atopile/cell-sim/elec/cell-card/parts/UNI_ROYAL_0603WAF1002T5E/R0603.STEP

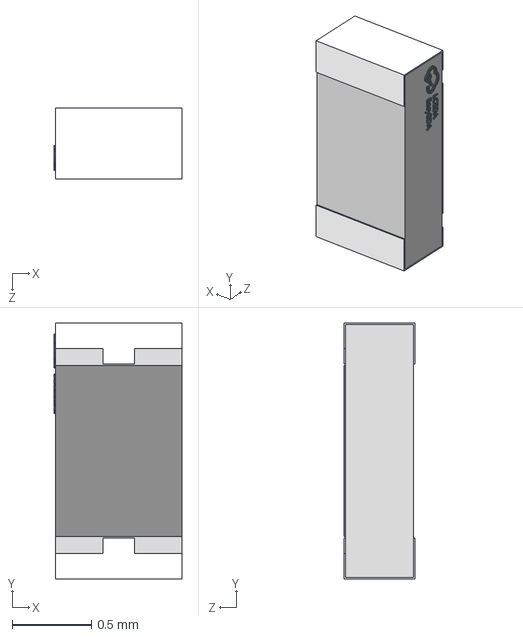
[picture p5: CAD file, 2026-02-27]
elec/cell-card/parts/UNI_ROYAL_0603WAF1002T5E/R0603.STEP
0.81 x 1.62 x 0.45 mm
