atopile/cell-sim/elec/cell-card/parts/UNI_ROYAL_0805W4F500MT5E/R0805_L2.0-W1.3-H0.6.step

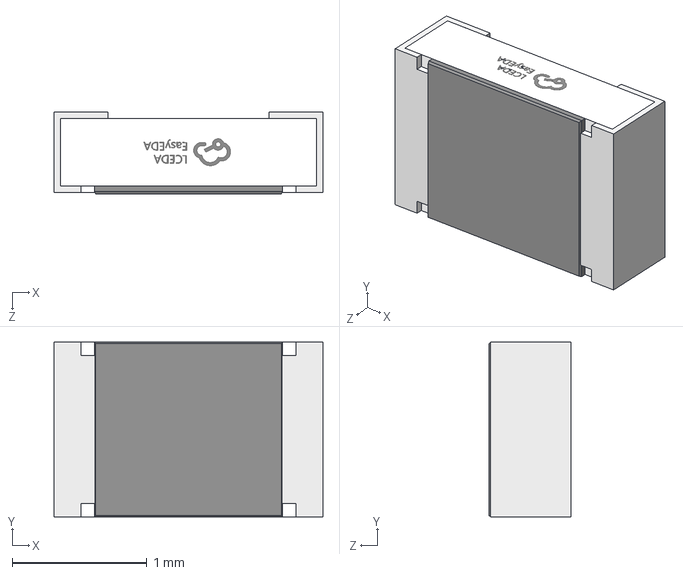
[picture p6: CAD file, 2026-02-27]
elec/cell-card/parts/UNI_ROYAL_0805W4F500MT5E/R0805_L2.0-W1.3-H0.6.step
2.00 x 1.30 x 0.61 mm
