atopile/cell-sim/elec/packages/buttons/parts/ALPSALPINE_SKRPACE010/KEY-SMD_4P-L4.2-W3.2-H2.5-LS4.6-P2.2.step

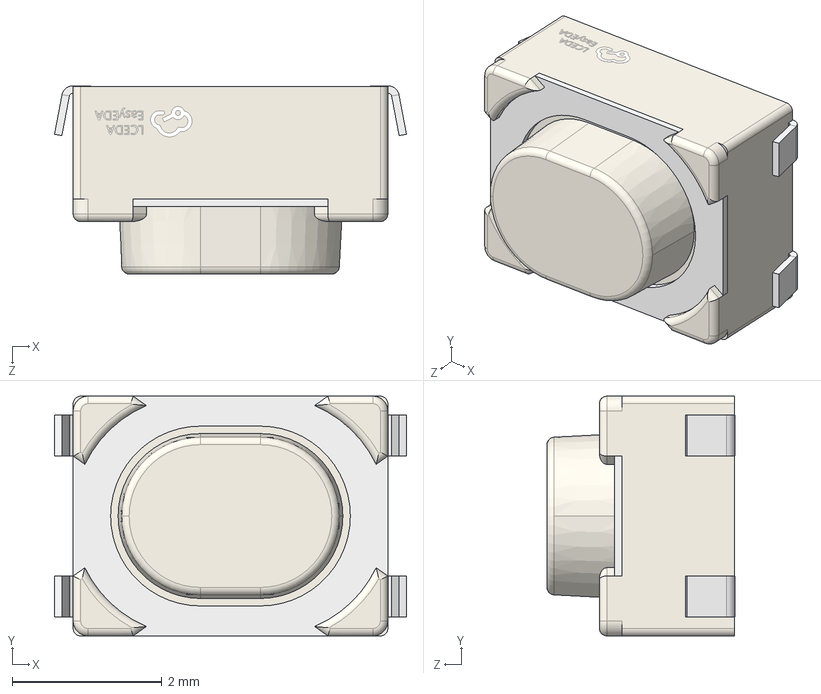
[picture p7: CAD file, 2026-03-11]
elec/packages/buttons/parts/ALPSALPINE_SKRPACE010/KEY-SMD_4P-L4.2-W3.2-H2.5-LS4.6-P2.2.step
4.70 x 3.20 x 2.51 mm
