atopile/cell-sim/elec/packages/buttons/parts/ALPSALPINE_SKTDLDE010/KEY-SMD_SKTDLDE010.step

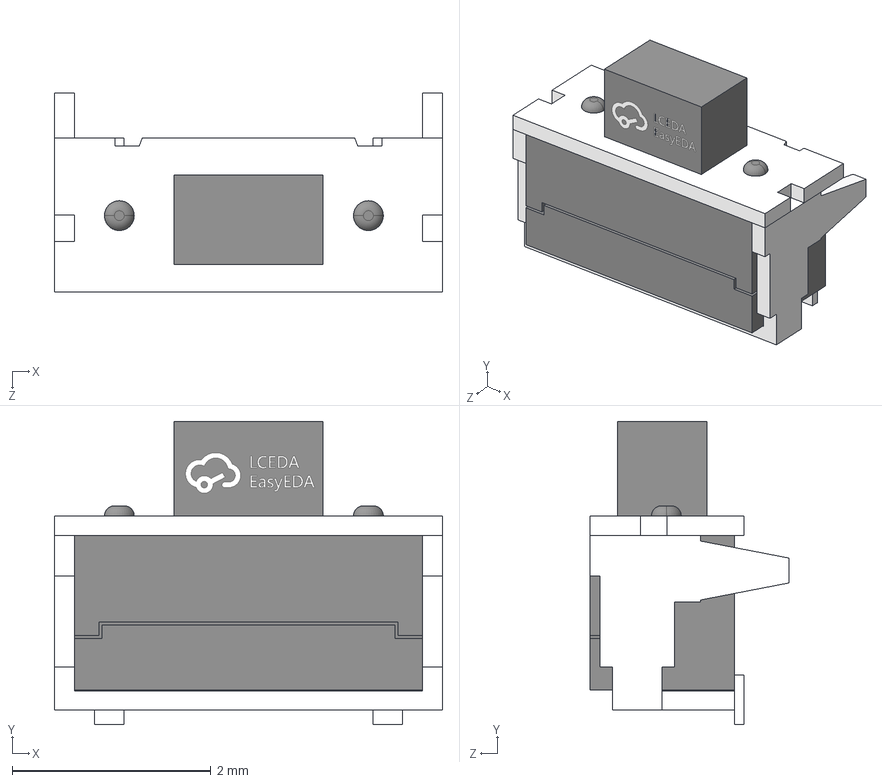
[picture p8: CAD file, 2026-03-11]
elec/packages/buttons/parts/ALPSALPINE_SKTDLDE010/KEY-SMD_SKTDLDE010.step
3.90 x 3.05 x 2.00 mm
