atopile/cell-sim/elec/packages/indicator-leds/parts/Diodes_Incorporated_B230A_13_F/SMA_L4.4-W2.6-LS5.0-RD.step

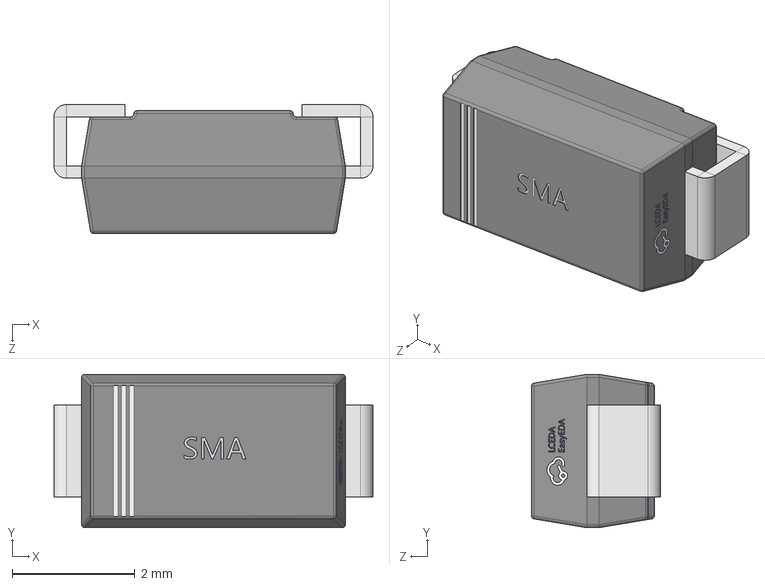
[picture p9: CAD file, 2026-03-11]
elec/packages/indicator-leds/parts/Diodes_Incorporated_B230A_13_F/SMA_L4.4-W2.6-LS5.0-RD.step
5.20 x 2.50 x 2.10 mm
