atopile/cell-sim/elec/packages/indicator-leds/parts/Hubei_KENTO_Elec_Blue_light_0603/LED0603-RD-YELLOW.STEP

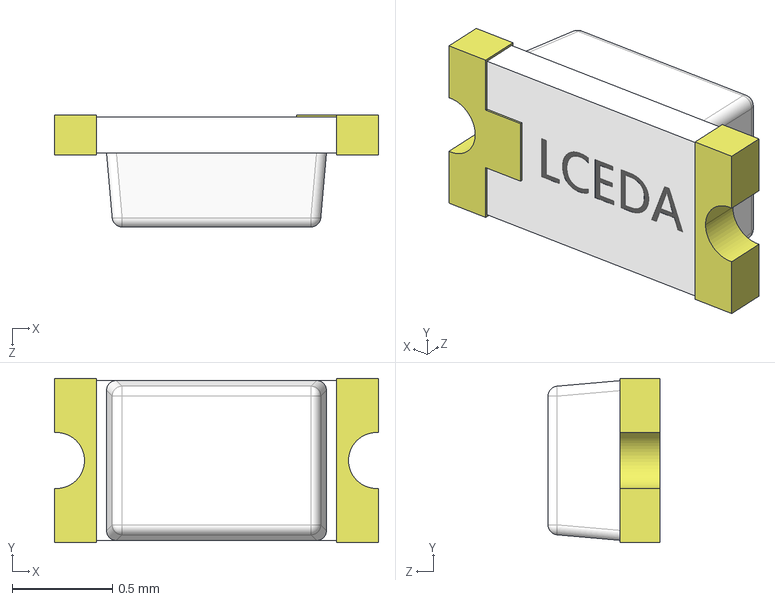
[picture p10: CAD file, 2026-03-11]
elec/packages/indicator-leds/parts/Hubei_KENTO_Elec_Blue_light_0603/LED0603-RD-YELLOW.STEP
1.62 x 0.82 x 0.56 mm
