atopile/cell-sim/elec/packages/indicator-leds/parts/Hubei_KENTO_Elec_KT_0603W/LED0603-RD_ORANGE.STEP

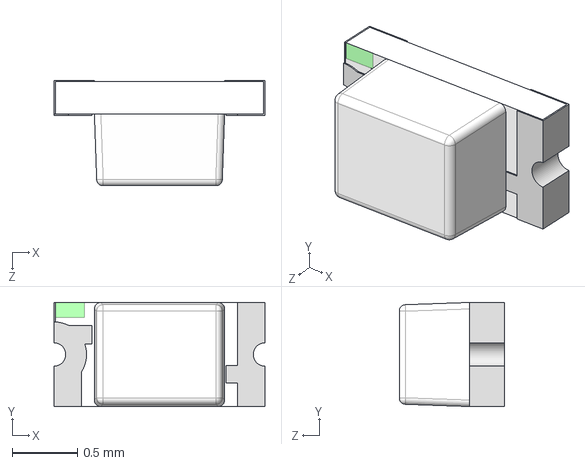
[picture p11: CAD file, 2026-03-11]
elec/packages/indicator-leds/parts/Hubei_KENTO_Elec_KT_0603W/LED0603-RD_ORANGE.STEP
1.62 x 0.8 x 0.81 mm
