atopile/cell-sim/elec/packages/indicator-leds/parts/Hubei_KENTO_Elec_KT_0603Y/LED0603-RD_BLUE.STEP

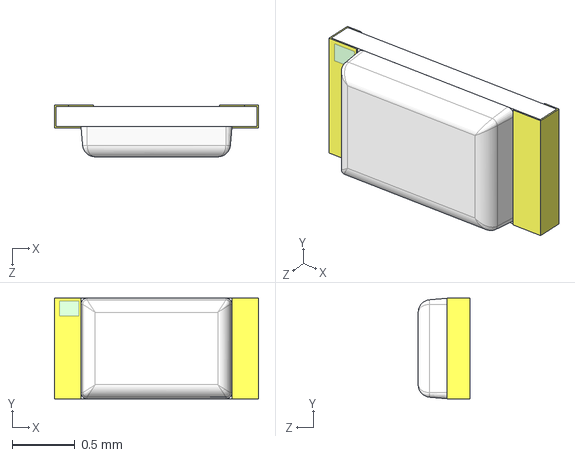
[picture p12: CAD file, 2026-03-11]
elec/packages/indicator-leds/parts/Hubei_KENTO_Elec_KT_0603Y/LED0603-RD_BLUE.STEP
1.62 x 0.8 x 0.41 mm
