atopile/cell-sim/elec/packages/indicator-leds/parts/MDD_Microdiode_Electronics_M7/SMA_L4.3-W2.6-LS5.2-RD.step

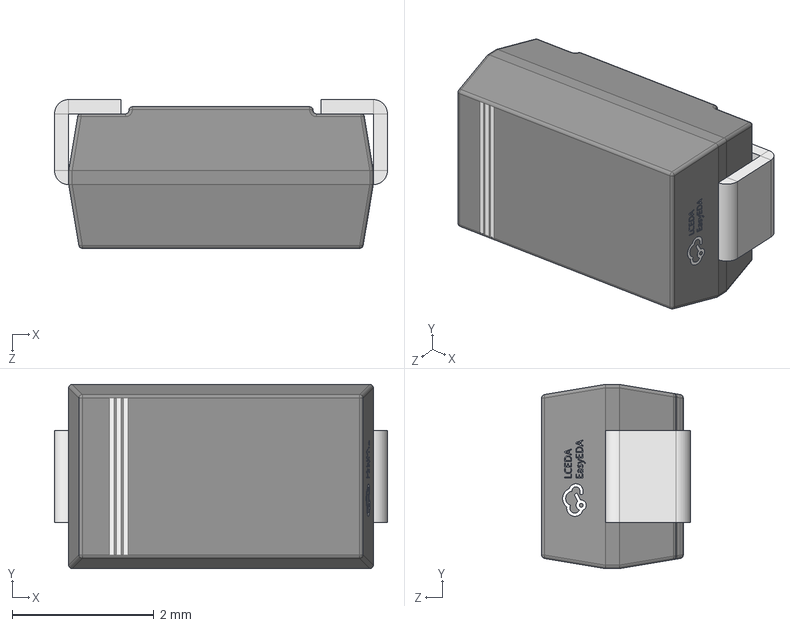
[picture p13: CAD file, 2026-03-11]
elec/packages/indicator-leds/parts/MDD_Microdiode_Electronics_M7/SMA_L4.3-W2.6-LS5.2-RD.step
4.70 x 2.60 x 2.10 mm
