atopile/cell-sim/elec/packages/microchip-emc2101/parts/Microchip_Tech_EMC2101_R_ACZL_TR/MSOP-8_L3.0-W3.0-H1.1-LS4.9-P0.65.step

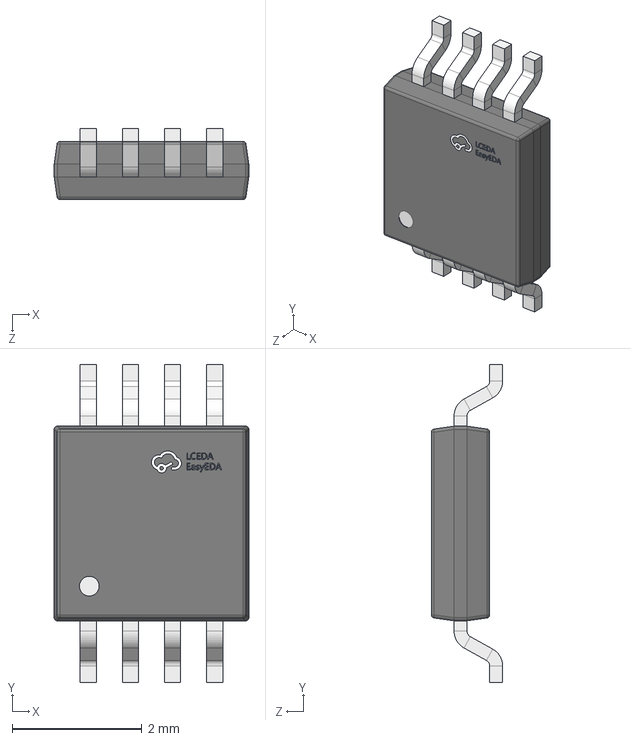
[picture p14: CAD file, 2026-03-11]
elec/packages/microchip-emc2101/parts/Microchip_Tech_EMC2101_R_ACZL_TR/MSOP-8_L3.0-W3.0-H1.1-LS4.9-P0.65.step
3.00 x 4.90 x 1.10 mm
