atopile/cell-sim/elec/packages/microchip-emc2101/parts/YAGEO_CC0603KRX7R9BB104/C0603_L1.6-W0.8-H0.8.step

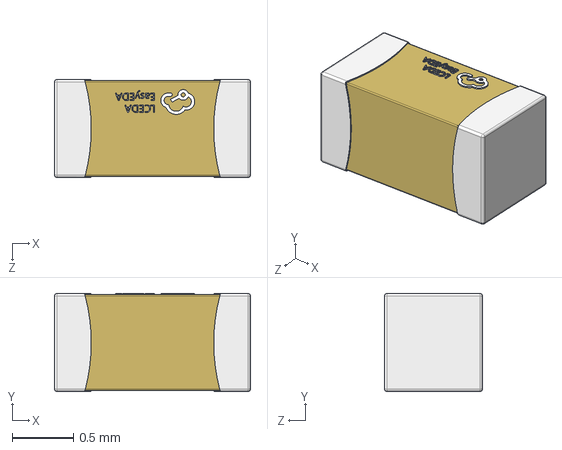
[picture p15: CAD file, 2026-02-27]
elec/packages/microchip-emc2101/parts/YAGEO_CC0603KRX7R9BB104/C0603_L1.6-W0.8-H0.8.step
1.60 x 0.8 x 0.8 mm
