atopile/cell-sim/elec/packages/microchip-lan8742a/parts/Microchip_Tech_LAN8742A_CZ_TR/QFN-24_L4.0-W4.0-P0.50-TL-EP2.1.step

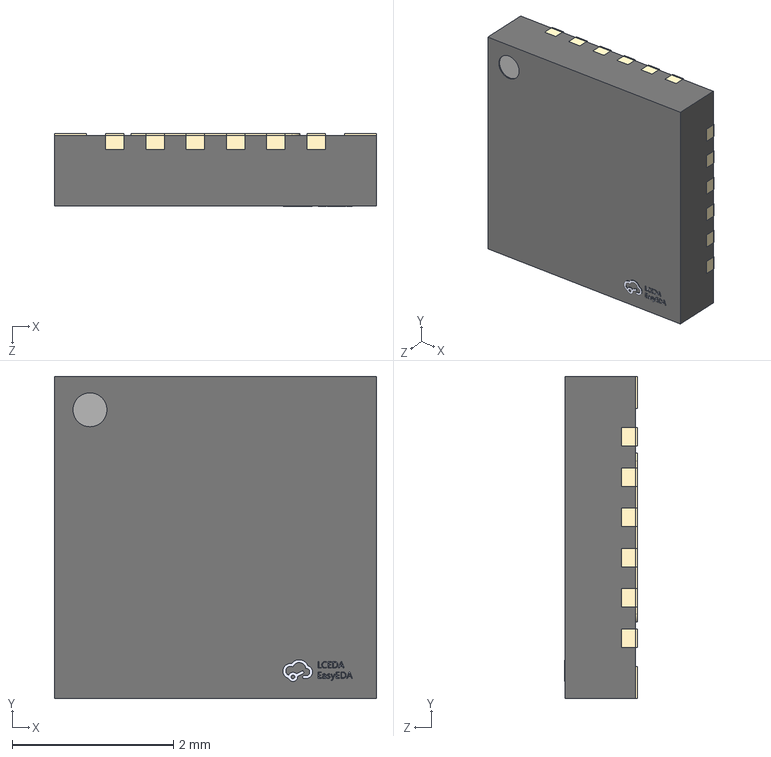
[picture p16: CAD file, 2026-02-27]
elec/packages/microchip-lan8742a/parts/Microchip_Tech_LAN8742A_CZ_TR/QFN-24_L4.0-W4.0-P0.50-TL-EP2.1.step
4.00 x 4.00 x 0.91 mm
