atopile/cell-sim/elec/packages/microchip-lan8742a/parts/Yangxing_Tech_X322525MRB4SI/OSC-SMD_4P-L3.2-W2.5-CJ13-320001210A20.step

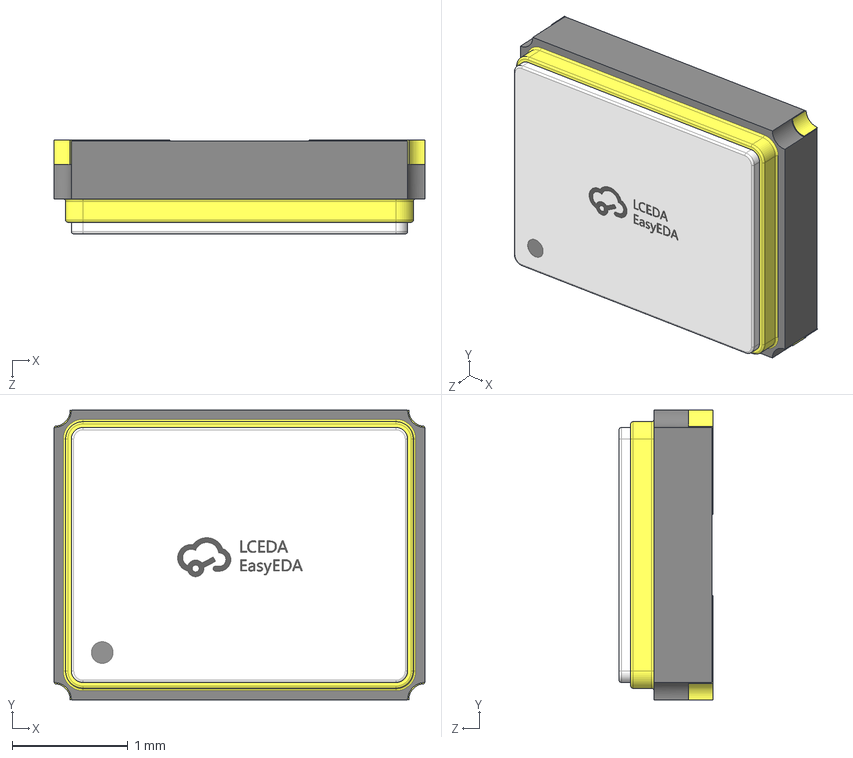
[picture p17: CAD file, 2026-02-27]
elec/packages/microchip-lan8742a/parts/Yangxing_Tech_X322525MRB4SI/OSC-SMD_4P-L3.2-W2.5-CJ13-320001210A20.step
3.20 x 2.50 x 0.811 mm
