atopile/cell-sim/elec/packages/microchip-mcp23017/parts/Microchip_Tech_MCP23017T_E_ML/QFN-28_L6.0-W6.0-P0.65-BL-EP3.7.step

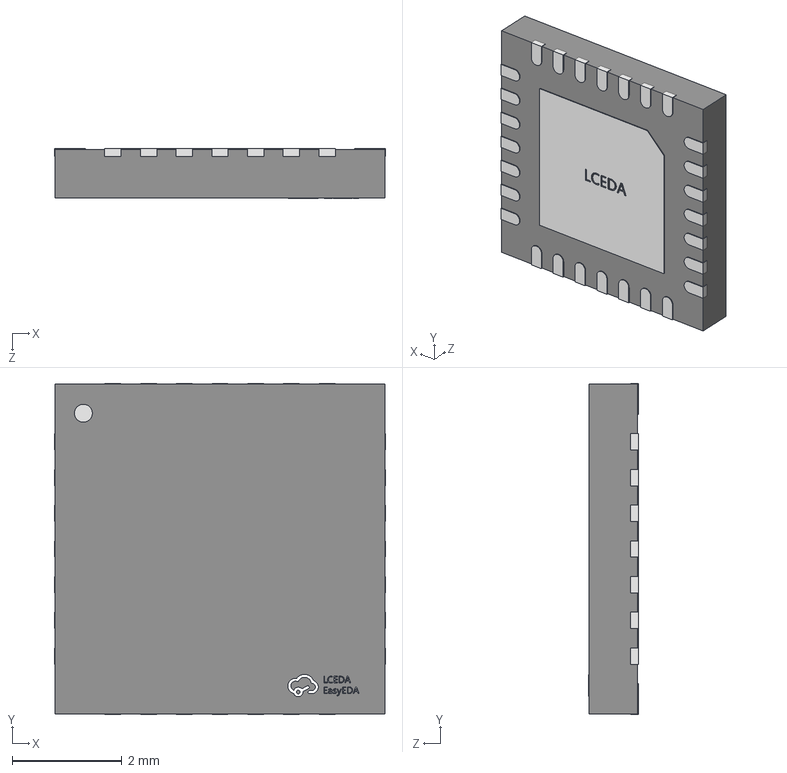
[picture p18: CAD file, 2026-03-11]
elec/packages/microchip-mcp23017/parts/Microchip_Tech_MCP23017T_E_ML/QFN-28_L6.0-W6.0-P0.65-BL-EP3.7.step
6.02 x 6.02 x 0.91 mm
