atopile/cell-sim/elec/packages/microchip-mcp3221/parts/Microchip_Tech_MCP3221A5T_I_OT/SOT-23-5_L2.9-W1.6-H1.1-LS2.8-P0.95.step

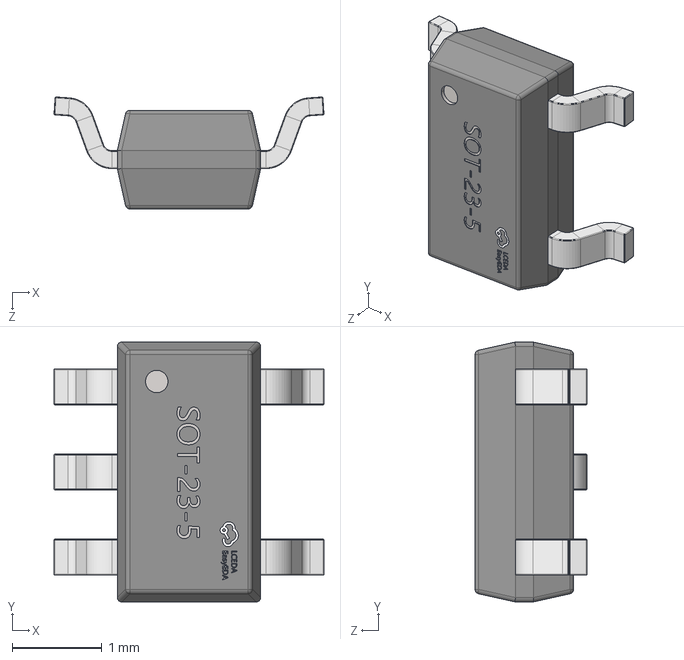
[picture p19: CAD file, 2026-02-27]
elec/packages/microchip-mcp3221/parts/Microchip_Tech_MCP3221A5T_I_OT/SOT-23-5_L2.9-W1.6-H1.1-LS2.8-P0.95.step
3.01 x 2.90 x 1.25 mm
