atopile/cell-sim/elec/packages/microchip-mcp4725/parts/Microchip_Tech_MCP3421A0T_E_CH/SOT-23-6_L2.9-W1.6-H1.5-LS2.8-P0.95.step

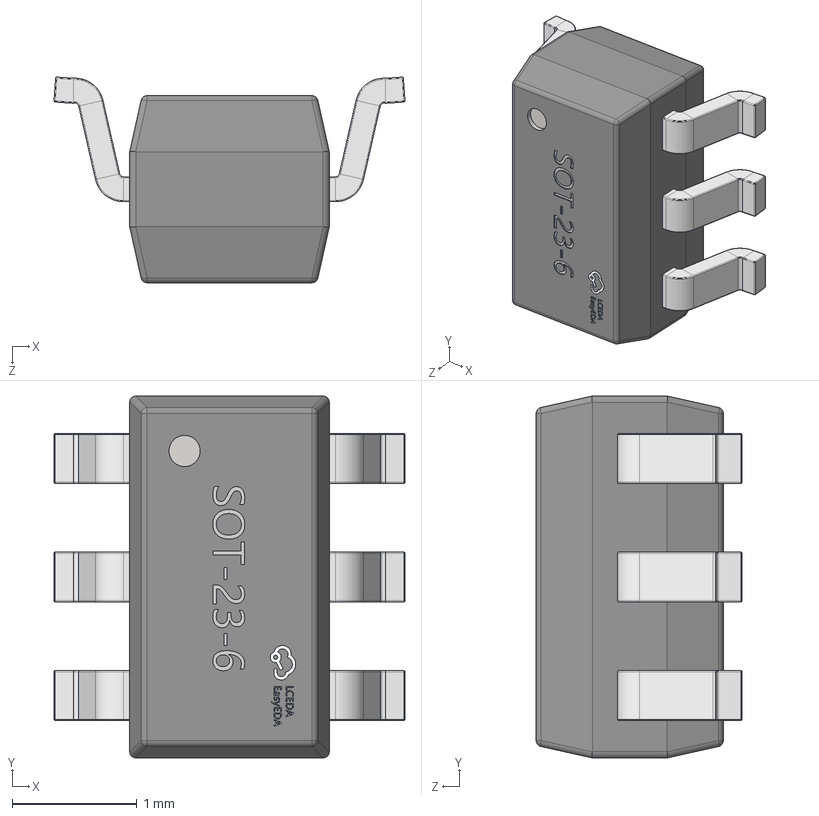
[picture p20: CAD file, 2026-02-27]
elec/packages/microchip-mcp4725/parts/Microchip_Tech_MCP3421A0T_E_CH/SOT-23-6_L2.9-W1.6-H1.5-LS2.8-P0.95.step
2.81 x 2.90 x 1.65 mm
