atopile/cell-sim/elec/packages/programming-headers/parts/Hanbo_Electronic_HB_PH9_12725PB2GOB/HDR-SMD_10P-P1.27-V-M-R2-C5-LS5.3.STEP

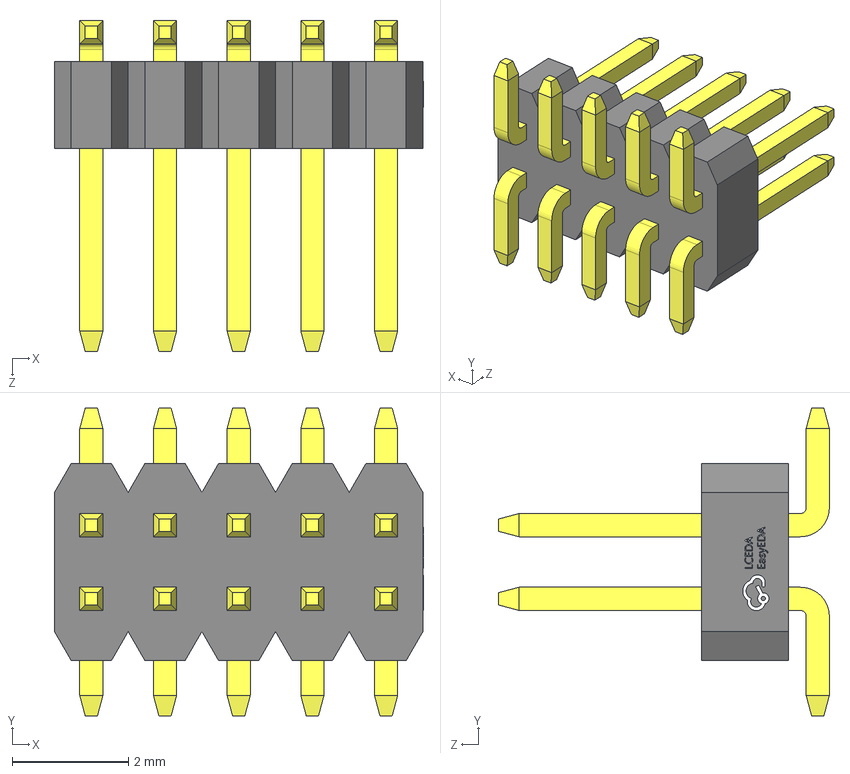
[picture p21: CAD file, 2026-03-11]
elec/packages/programming-headers/parts/Hanbo_Electronic_HB_PH9_12725PB2GOB/HDR-SMD_10P-P1.27-V-M-R2-C5-LS5.3.STEP
6.36 x 5.30 x 5.70 mm
