atopile/cell-sim/elec/packages/programming-headers/parts/Liansheng_BH_00019/CONN-SMD_20P-P2.54_BH-00019.step

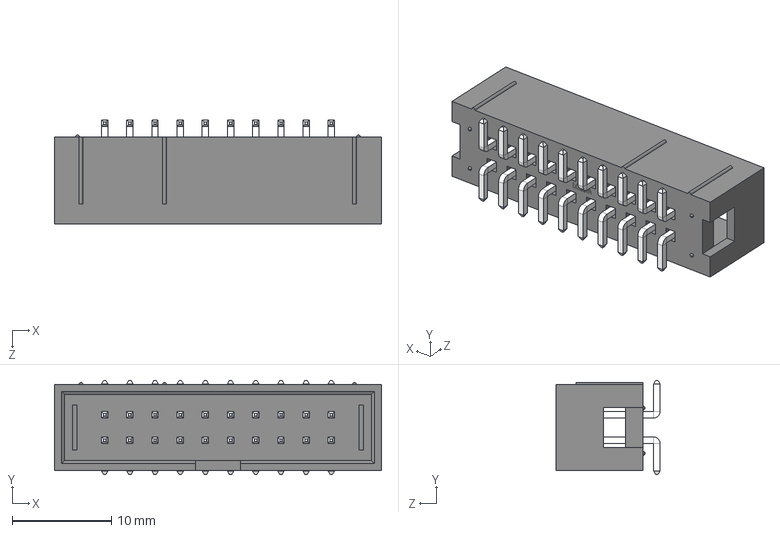
[picture p22: CAD file, 2026-03-11]
elec/packages/programming-headers/parts/Liansheng_BH_00019/CONN-SMD_20P-P2.54_BH-00019.step
33.0 x 9.50 x 10.5 mm
