atopile/cell-sim/elec/packages/programming-headers/parts/XFCN_BH254VS_10P/IDC-SMD_10P-P2.54-V-R2-C5-S9.50.step

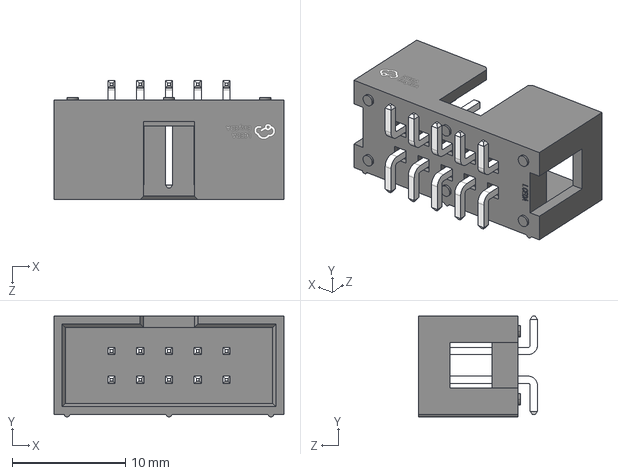
[picture p23: CAD file, 2026-03-11]
elec/packages/programming-headers/parts/XFCN_BH254VS_10P/IDC-SMD_10P-P2.54-V-R2-C5-S9.50.step
20.3 x 8.90 x 10.5 mm
