atopile/cell-sim/elec/packages/pulse-hx1198/parts/Pulse_Elec_HX1198NLT/SMD-16_L12.7-W7.2-P1.27-LS9.5-BL.STEP

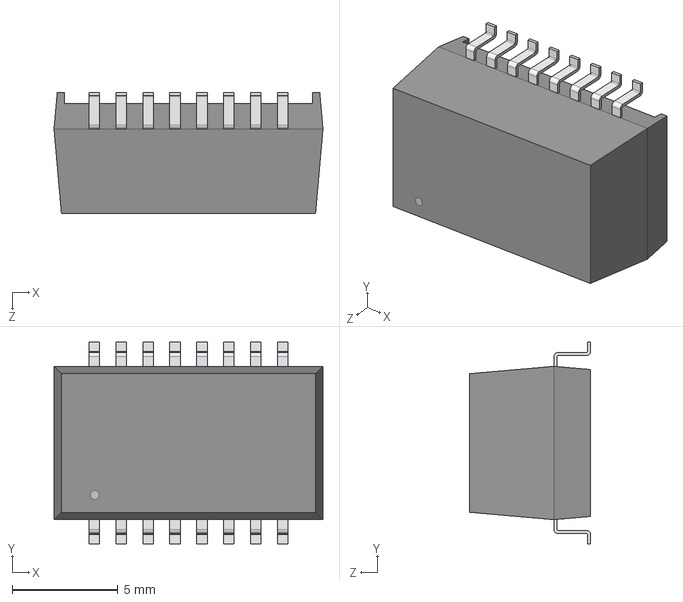
[picture p24: CAD file, 2026-02-28]
elec/packages/pulse-hx1198/parts/Pulse_Elec_HX1198NLT/SMD-16_L12.7-W7.2-P1.27-LS9.5-BL.STEP
12.7 x 9.52 x 5.74 mm
