atopile/cell-sim/elec/packages/relays/parts/Alpha___Omega_Semicon_AO3400A/SOT-23-3P_L2.9-W1.3-H1.0-LS2.4-P0.95.step

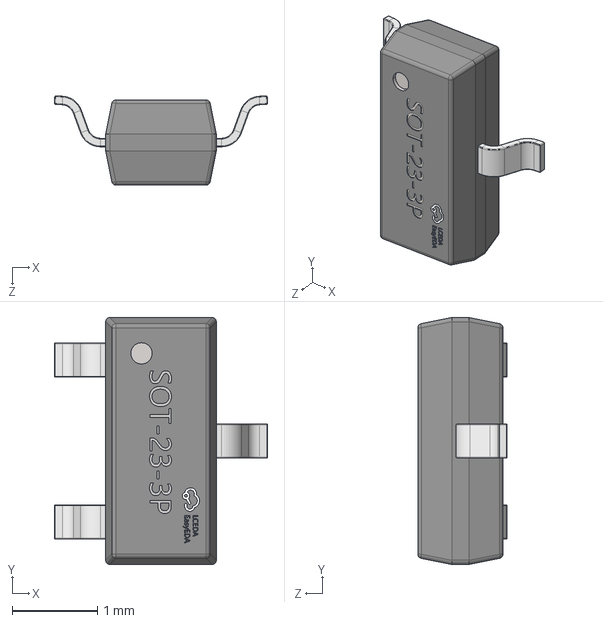
[picture p25: CAD file, 2026-02-28]
elec/packages/relays/parts/Alpha___Omega_Semicon_AO3400A/SOT-23-3P_L2.9-W1.3-H1.0-LS2.4-P0.95.step
2.51 x 2.90 x 1.05 mm
