atopile/cell-sim/elec/packages/relays/parts/Omron_Electronics_G5Q_1A4_DC24/RELAY-TH_G5Q-1A4.step

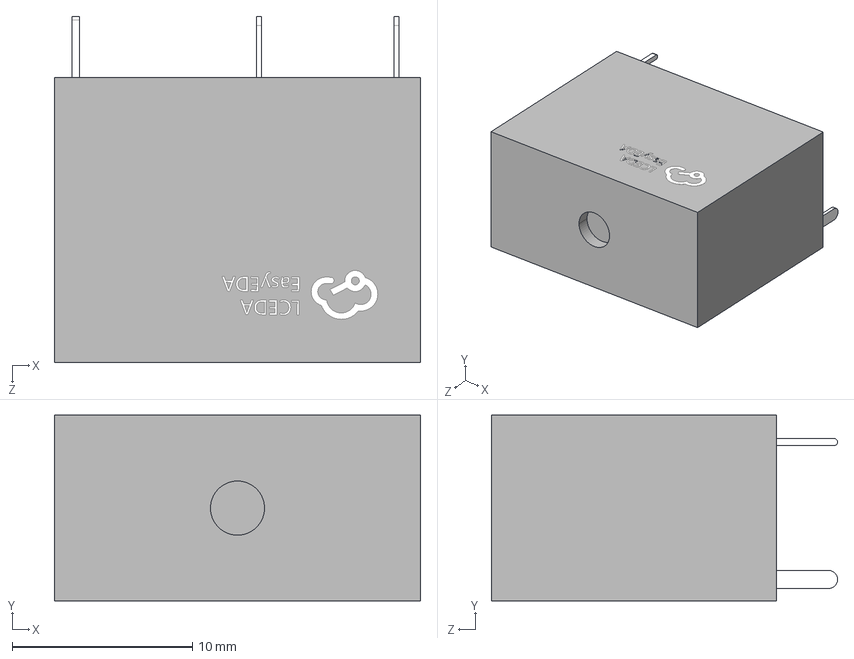
[picture p26: CAD file, 2026-02-28]
elec/packages/relays/parts/Omron_Electronics_G5Q_1A4_DC24/RELAY-TH_G5Q-1A4.step
20.3 x 10.3 x 19.2 mm
