atopile/cell-sim/elec/packages/relays/parts/Omron_Electronics_G6K_2F_Y_TR_DC3/SMD-8_L10.0-W6.5-H5.4-LS7.8-P2.2.step

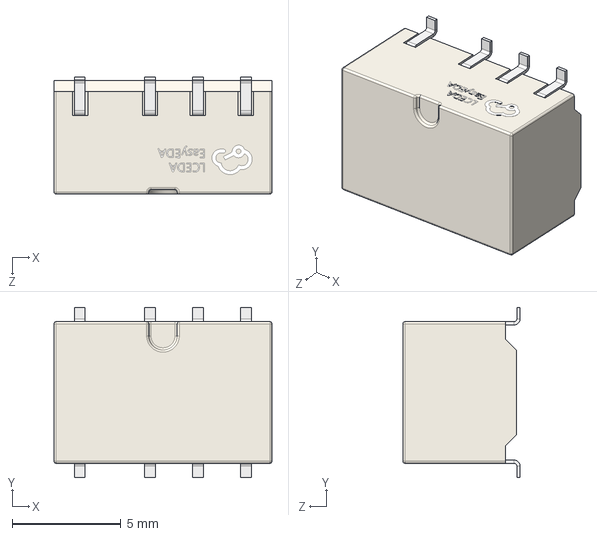
[picture p27: CAD file, 2026-03-11]
elec/packages/relays/parts/Omron_Electronics_G6K_2F_Y_TR_DC3/SMD-8_L10.0-W6.5-H5.4-LS7.8-P2.2.step
10.0 x 7.80 x 5.38 mm
