atopile/cell-sim/elec/packages/rj45-connectors/parts/Ckmtw_R_RJ45S08P_C000/RJ45-TH_R-RJ45S08P-C000.STEP

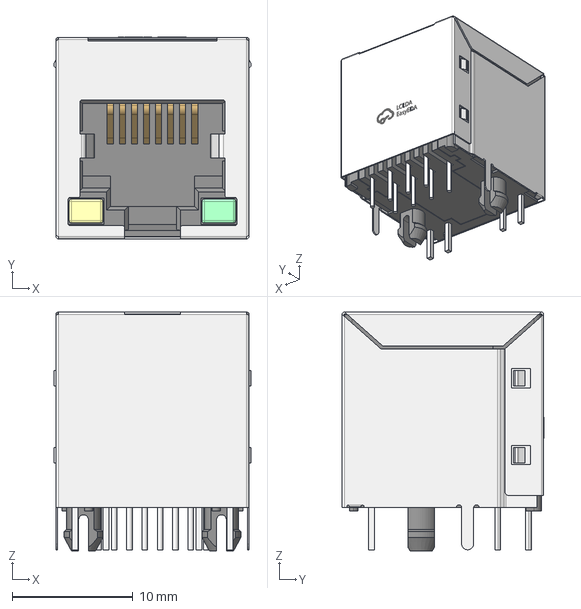
[picture p28: CAD file, 2026-03-11]
elec/packages/rj45-connectors/parts/Ckmtw_R_RJ45S08P_C000/RJ45-TH_R-RJ45S08P-C000.STEP
16.3 x 16.7 x 19.8 mm
