atopile/cell-sim/elec/packages/rj45-connectors/parts/HCTL_HC_RJ45_055_7/RJ45-SMD_HC-RJ45-055-7_1.STEP

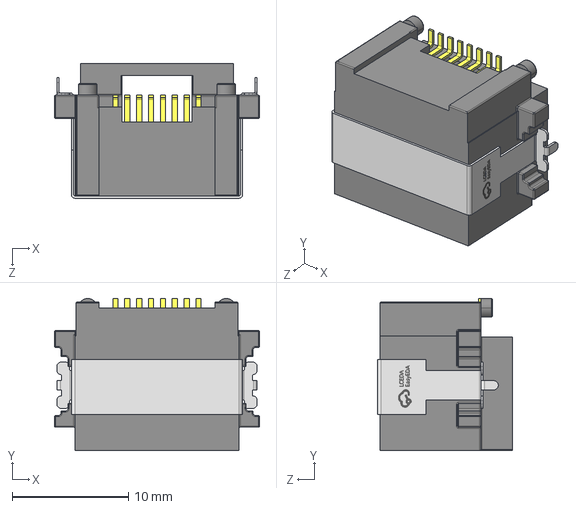
[picture p29: CAD file, 2026-03-11]
elec/packages/rj45-connectors/parts/HCTL_HC_RJ45_055_7/RJ45-SMD_HC-RJ45-055-7_1.STEP
17.6 x 13.0 x 11.6 mm
