atopile/cell-sim/elec/packages/rpi-cm5/parts/Sinhoo_SMTSO2515CTJ/SMD_BD5.6-D4.1.STEP

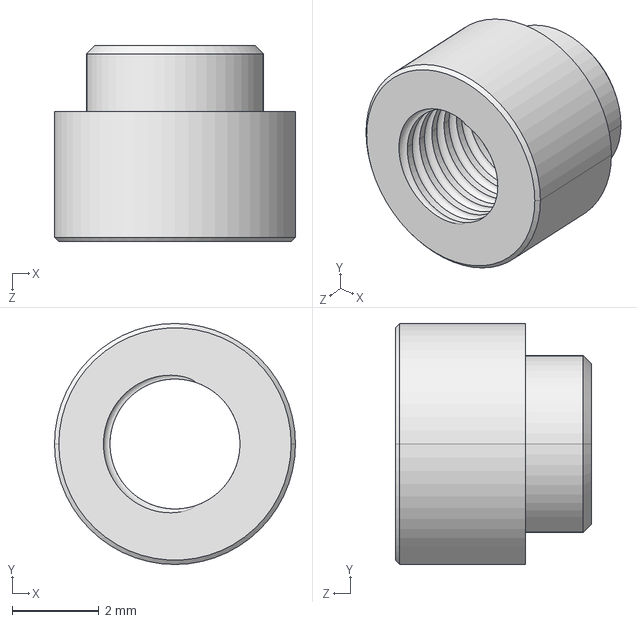
[picture p30: CAD file, 2026-03-11]
elec/packages/rpi-cm5/parts/Sinhoo_SMTSO2515CTJ/SMD_BD5.6-D4.1.STEP
5.56 x 5.56 x 4.53 mm
