atopile/cell-sim/elec/packages/st-stm32h723/parts/STMicroelectronics_STM32H723VGH6/TFBGA-100_L8.0-W8.0-R10-C10-P0.80-BL.STEP

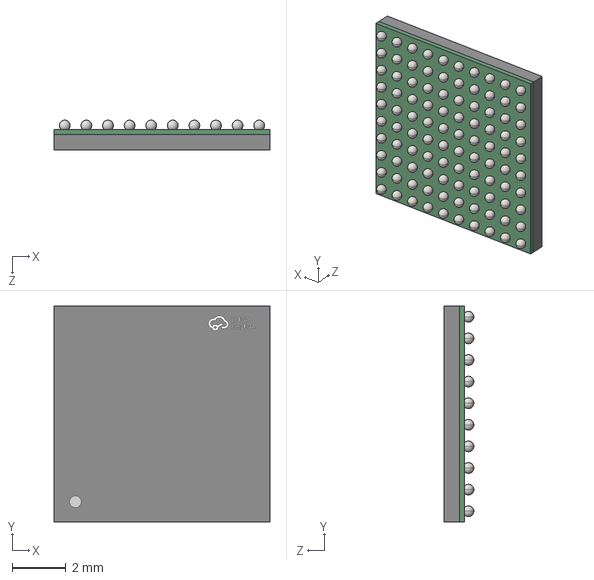
[picture p31: CAD file, 2026-02-27]
elec/packages/st-stm32h723/parts/STMicroelectronics_STM32H723VGH6/TFBGA-100_L8.0-W8.0-R10-C10-P0.80-BL.STEP
8.00 x 8.00 x 1.10 mm
