atopile/cell-sim/elec/packages/ti-tps54560x/layouts/usage/usage.kicad_pcb

## KiCad design elec/packages/ti-tps54560x/layouts/usage/usage.kicad_pcb (2026-03-11)

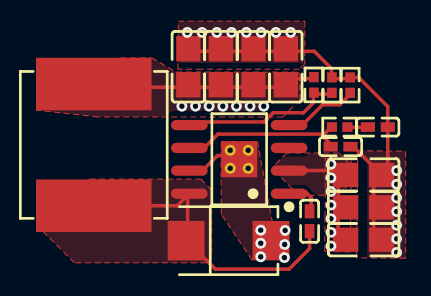
[picture p40: board elec/packages/ti-tps54560x/layouts/usage/usage.kicad_pcb from above]

Board: 2 copper layers, 17 parts (0 on the bottom side), 9 nets.

Parts:
C1: 100nF ±10% 50V X7R; C0402
C2: 4.7nF ±5% 50V X7R; C0402
C3: 10pF ±5% 50V C0G; C0402
C4, C5, C6: 10µF ±10% 50V X5R; C0805
C7, C8, C9, C10: 22µF ±20% 25V X5R; C0805
D1: SMB_L4.6-W3.6-LS5.3-RD
L1: IND-SMD_L8.0-W8.0_SWPA8040S
R1: 23.7kΩ ±1% 62.5mW; R0402
R2, R3: 10kΩ ±1% 62.5mW; R0402
R4: 162kΩ ±1% 62.5mW; R0402
U1: SOIC-8_L5.0-W4.0-P1.27-LS6.0-BL-EP2.0

Connections:
BOOT: C1.1, U1.1
COMP: C3.1, R1.1, U1.6
GND: C2.2, C3.2, C4.2, C5.2, C6.2, C7.2, C8.2, C9.2, C10.2, D1.2, R2.2, R4.2, U1.7, U1.9
RT_CLK: R4.1, U1.4
VDIV_OUTPUT: R2.1, R3.2, U1.5
cathode: C1.2, D1.1, L1.1, U1.8
net: C2.1, R1.2
power_in-VCC: C4.1, C5.1, C6.1, U1.2
power_out-VCC: C7.1, C8.1, C9.1, C10.1, L1.2, R3.1
