atopile/cell-sim/elec/packages/rpi-cm5/layouts/default/default.kicad_pcb

## KiCad design elec/packages/rpi-cm5/layouts/default/default.kicad_pcb (2026-03-11)

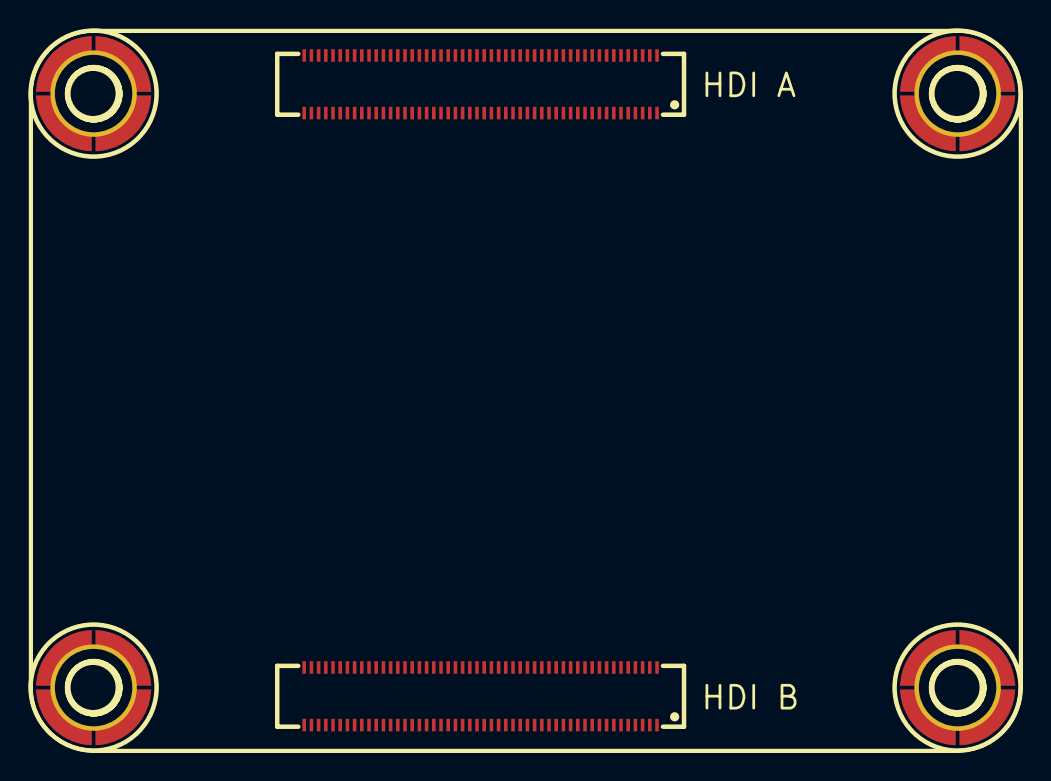
[picture p41: board elec/packages/rpi-cm5/layouts/default/default.kicad_pcb from above]

Board: 4 copper layers, 7 parts (0 on the bottom side), 5 nets, no tracks yet.

Parts:
CN1, CN2: CONN-SMD_DF40C-100DS-0.4V-51
U1, U2, U3, U4: SMD_BD5.6-D4.1
U5: cm5

Connections:
lv: CN1.1, CN1.4, CN1.7, CN1.11, CN1.16, CN1.21, CN1.26, CN1.30, CN1.33, CN1.37, CN1.49, CN1.65, CN1.68, CN1.71, CN1.74, CN1.79, CN1.84, CN1.89, CN1.94, CN1.97, CN1.100, CN2.4, CN2.7, CN2.10, CN2.13, CN2.16, CN2.22, CN2.28, CN2.31, CN2.34, CN2.37, CN2.40, CN2.43, CN2.46, CN2.49, CN2.52, CN2.55, CN2.58, CN2.61, CN2.64, CN2.67, CN2.70, CN2.73, CN2.82, CN2.85, CN2.88, CN2.91, CN2.94, CN2.97
power_1v8-hv: CN1.44, CN1.45
power_3v3-hv: CN1.42, CN1.43
power_3v3-lv: U1.1, U1.2, U1.3, U1.4, U1.5, U2.1, U2.2, U2.3, U2.4, U2.5, U3.1, U3.2, U3.3, U3.4, U3.5, U4.1, U4.2, U4.3, U4.4, U4.5
power_5v-hv: CN1.57, CN1.58, CN1.59, CN1.60, CN1.61, CN1.62
