atopile/cell-sim/elec/packages/ylptech-byyxx/layouts/default/default.kicad_pcb

## KiCad design elec/packages/ylptech-byyxx/layouts/default/default.kicad_pcb (2026-03-11)

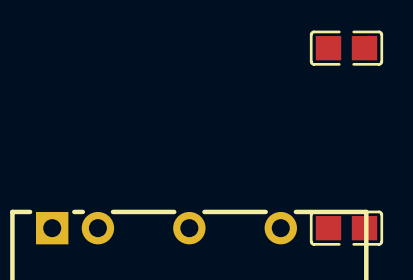
[picture p42: board elec/packages/ylptech-byyxx/layouts/default/default.kicad_pcb from above]

Board: 2 copper layers, 3 parts (0 on the bottom side), 4 nets, no tracks yet.

Parts:
C1, C2: [capacitance: unknown]; C0805
U1: PWRM-TH_BXXXXS-2WR3

Connections:
hv: C1.1, U1.1
lv: C1.2, U1.2
output_cap-power-hv: C2.1, U1.6
output_cap-power-lv: C2.2, U1.4
