atopile/cell-sim/elec/packages/usb-connectors/layouts/default/default.kicad_pcb

## KiCad design elec/packages/usb-connectors/layouts/default/default.kicad_pcb (2026-03-11)

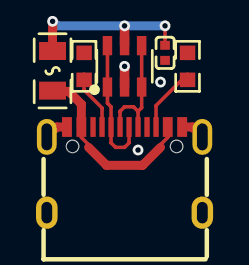
[picture p43: board elec/packages/usb-connectors/layouts/default/default.kicad_pcb from above]

Board: 2 copper layers, 6 parts (0 on the bottom side), 7 nets.

Parts:
C2: 100nF; C0402
D1: SOT-23-6_L2.9-W1.6-P0.95-LS2.8-BL
F2: F0805
R1, R2: 10kΩ; R0603
X1: USB-C-SMD_TYPE-C-6PIN-2MD-073

Connections:
4: R1.1, X1.4
10: R2.1, X1.10
DATA_N: D1.1, D1.6, X1.5, X1.7
DATA_P: D1.3, D1.4, X1.6, X1.8
hv: F2.1, X1.2, X1.11
lv: C2.2, D1.2, R1.2, R2.2, X1.1, X1.12, X1.13, X1.14, X1.15, X1.16
power-hv: C2.1, D1.5, F2.2
