atopile/cell-sim/elec/packages/usb-connectors/layouts/usage/usage.kicad_pcb

## KiCad design elec/packages/usb-connectors/layouts/usage/usage.kicad_pcb (2026-03-11)

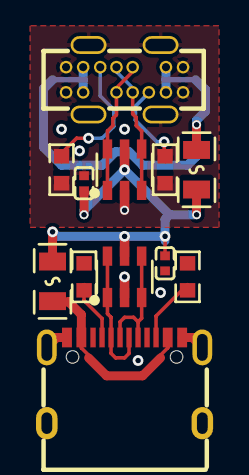
[picture p44: board elec/packages/usb-connectors/layouts/usage/usage.kicad_pcb from above]

Board: 2 copper layers, 12 parts (0 on the bottom side), 12 nets.

Parts:
C2, C4: 100nF; C0402
D1, D2: SOT-23-6_L2.9-W1.6-P0.95-LS2.8-BL
F2, F4: F0805
R1, R2, R3, R4: 10kΩ; R0603
USB1: USB-C-SMD_TYPE-C-6PIN-2MD-073
USBC1: USB-C-TH_TYPE-C-USB-14P

Connections:
4: R1.1, USB1.4
5: R4.1, USBC1.5
10: R2.1, USB1.10
12: R3.1, USBC1.12
DATA_N: D1.1, D1.6, USB1.5, USB1.7
DATA_P: D1.3, D1.4, USB1.6, USB1.8
connector-power_vbus-hv: F2.1, USB1.2, USB1.11
connector-power_vbus-hv-1: F4.1, USBC1.2, USBC1.6, USBC1.9, USBC1.13
hv: C2.1, C4.1, D1.5, D2.5, F2.2, F4.2
lv: C2.2, C4.2, D1.2, D2.2, R1.2, R2.2, R3.2, R4.2, USB1.1, USB1.12, USB1.13, USB1.14, USB1.15, USB1.16, USBC1.0, USBC1.1, USBC1.7, USBC1.8, USBC1.14, USBC1.15, USBC1.16, USBC1.17
usb_connector_vertical-usb-DATA_N: D2.1, D2.6, USBC1.3, USBC1.10
usb_connector_vertical-usb-DATA_P: D2.3, D2.4, USBC1.4, USBC1.11
