atopile/cell-sim/elec/packages/ti-cd74hc4067sm/layouts/usage/usage.kicad_pcb

## KiCad design elec/packages/ti-cd74hc4067sm/layouts/usage/usage.kicad_pcb (2026-03-11)

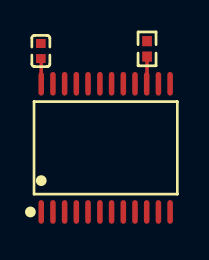
[picture p45: board elec/packages/ti-cd74hc4067sm/layouts/usage/usage.kicad_pcb from above]

Board: 2 copper layers, 3 parts (0 on the bottom side), 3 nets.

Parts:
C1: 1F; C0402
R1: 10000Ω; R0402
U1: SSOP-24_L8.1-W5.3-P0.65-LS7.8-BL

Connections:
hv: C1.1, U1.8, U1.24
lv: C1.2, R1.1, U1.9, U1.12
nE: R1.2, U1.15
