atopile/cell-sim/elec/packages/ti-ads131m04/layouts/usage/usage.kicad_pcb

## KiCad design elec/packages/ti-ads131m04/layouts/usage/usage.kicad_pcb (2026-03-11)

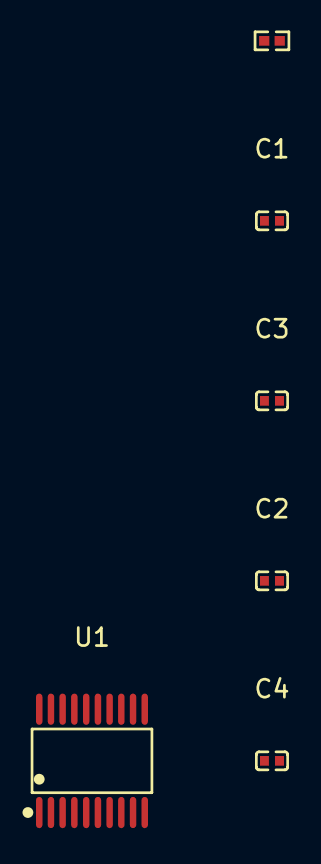
[picture p46: board elec/packages/ti-ads131m04/layouts/usage/usage.kicad_pcb from above]

Board: 2 copper layers, 6 parts (0 on the bottom side), 4 nets, no tracks yet.

Parts:
C1, C3: 1µF; C0402
C2, C4: 100nF; C0402
R1: 10kΩ; R0402
U1: TSSOP-20_L6.5-W4.4-P0.65-LS6.4-BL

Connections:
cap_bypass-power-hv: C3.1, U1.18
hv: C1.1, C2.1, C4.1, R1.2, U1.1, U1.20
lv: C1.2, C2.2, C3.2, C4.2, U1.2, U1.19
nSYNC_nRESET: R1.1, U1.11
