atopile/cell-sim/elec/packages/rj45-connectors/layouts/default/default.kicad_pcb

## KiCad design elec/packages/rj45-connectors/layouts/default/default.kicad_pcb (2026-03-11)

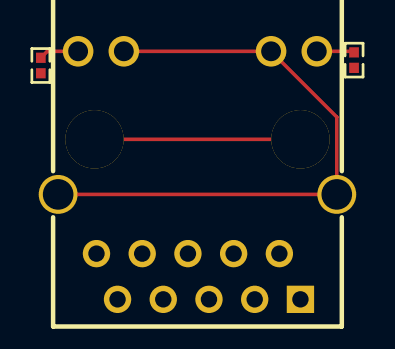
[picture p47: board elec/packages/rj45-connectors/layouts/default/default.kicad_pcb from above]

Board: 2 copper layers, 3 parts (0 on the bottom side), 3 nets.

Parts:
R1, R2: 470.0Ω; R0402
U1: RJ45-TH_HR911130A

Connections:
11: R2.2, U1.11
14: R1.2, U1.14
lv: U1.12, U1.13, U1.SHIELD0, U1.SHIELD1
