atopile/cell-sim/elec/packages/rj45-connectors/layouts/usage/usage.kicad_pcb

## KiCad design elec/packages/rj45-connectors/layouts/usage/usage.kicad_pcb (2026-03-11)

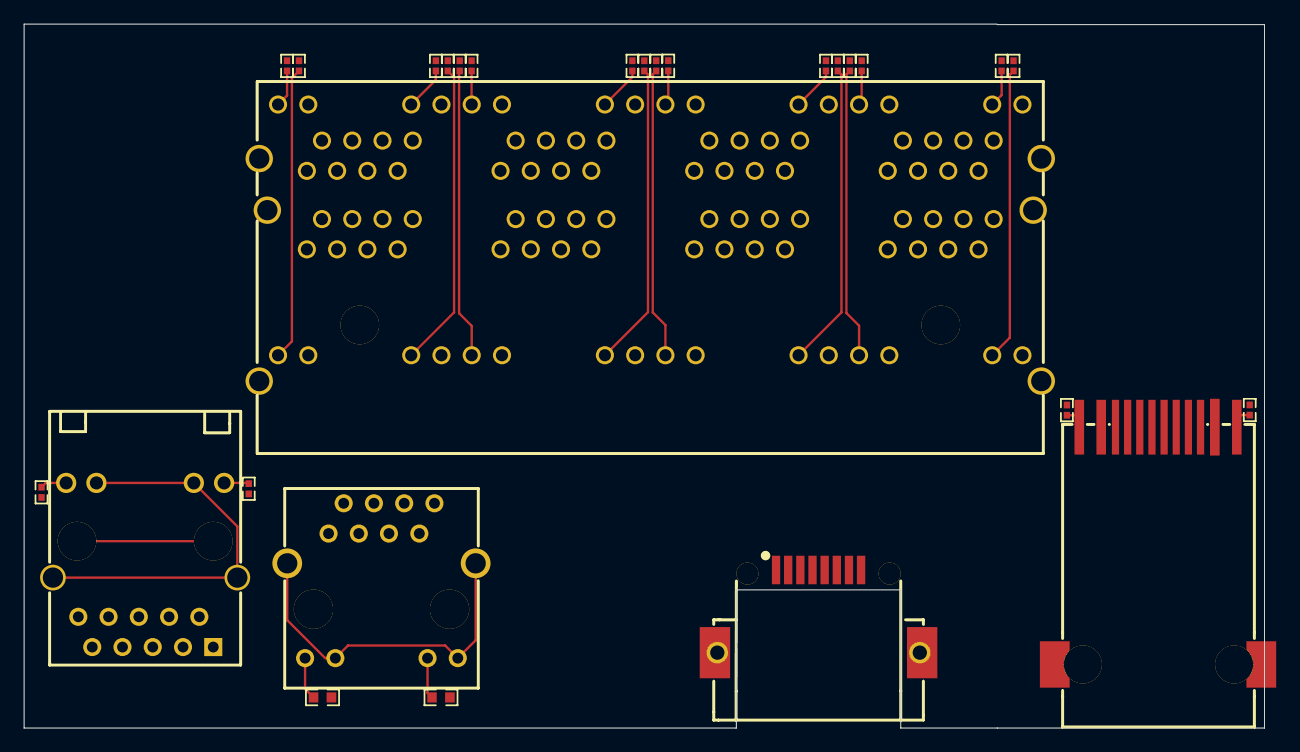
[picture p48: board elec/packages/rj45-connectors/layouts/usage/usage.kicad_pcb from above]

Board: 2 copper layers, 104.1 x 59.1 mm, 27 parts (0 on the bottom side), 24 nets.

Parts:
R1, R2, R5, R6, R7, R8, R9, R10, R11, R12, R13, R14, R15, R16, R17, R18, R19, R20, R21, R22: 470Ω; R0402
R3, R4: 10kΩ; R0603
RJ1: RJ45-TH_HR911130A
RJ2: RJ45-SMD_BS-R250210
U1: RJ45-TH_R-RJ45S08P-C000
U2: RJ45-SMD_HC-RJ45-055-7_1
U3: RJ45-TH_HC-RJ45-059C-2X4-1

Connections:
10: R13.2, U3.10
11: R2.2, RJ1.11
12: R5.2, U3.12
14: R1.2, RJ1.14
22: R14.2, U3.22
24: R6.2, U3.24
34: R15.2, U3.34
36: R7.2, U3.36
46: R16.2, U3.46
48: R8.2, U3.48
57: R9.2, U3.57
59: R17.2, U3.59
69: R10.2, U3.69
71: R18.2, U3.71
81: R11.2, U3.81
83: R19.2, U3.83
93: R12.2, U3.93
95: R20.2, U3.95
CT: RJ2.3, RJ2.4
Gpos: R4.2, U1.11
L_LED_Gpos: R22.2, RJ2.12
R_LEDYpos: R21.2, RJ2.9
Ypos: R3.2, U1.9
lv: RJ1.12, RJ1.13, RJ1.SHIELD0, RJ1.SHIELD1, RJ2.8, RJ2.10, RJ2.11, RJ2.13, RJ2.14, U1.10, U1.12, U1.13, U1.14, U2.9, U2.10, U3.9, U3.11, U3.21, U3.23, U3.33, U3.35, U3.45, U3.47, U3.58, U3.60, U3.70, U3.72, U3.82, U3.84, U3.94, U3.96, U3.97, U3.98, U3.99, U3.100, U3.101, U3.102
