atopile/cell-sim/elec/packages/indicator-leds/layouts/usage/usage.kicad_pcb

## KiCad design elec/packages/indicator-leds/layouts/usage/usage.kicad_pcb (2026-03-11)

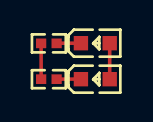
[picture p49: board elec/packages/indicator-leds/layouts/usage/usage.kicad_pcb from above]

Board: 2 copper layers, 4 parts (0 on the bottom side), 4 nets.

Parts:
LED1, LED2: LED0603-RD
R1, R2: 4.7kΩ; R0402

Connections:
anode: LED1.2, LED2.2
cathode: LED1.1, R1.1
lv: R1.2, R2.2
red_led-cathode: LED2.1, R2.1
