atopile/cell-sim/elec/packages/microchip-mcp23017/layouts/usage/usage.kicad_pcb

## KiCad design elec/packages/microchip-mcp23017/layouts/usage/usage.kicad_pcb (2026-03-11)

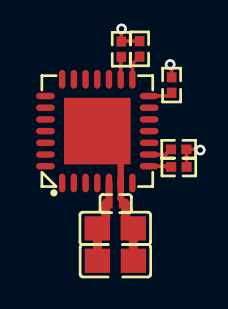
[picture p50: board elec/packages/microchip-mcp23017/layouts/usage/usage.kicad_pcb from above]

Board: 2 copper layers, 9 parts (0 on the bottom side), 7 nets.

Parts:
C1, C2: 10µF; C0805
C3: 100nF; C0402
R1, R2, R3, R4, R5: 10kΩ; R0402
U1: QFN-28_L6.0-W6.0-P0.65-BL-EP3.7

Connections:
INTA: R1.1, U1.16
INTB: R2.1, U1.15
SCL: R4.1, U1.8
SDA: R5.1, U1.9
hv: C1.1, C2.1, C3.1, R1.2, R2.2, R3.2, R4.2, R5.2, U1.5
lv: C1.2, C2.2, C3.2, U1.6, U1.11, U1.12, U1.13, U1.29
nRESET: R3.1, U1.14
