atopile/cell-sim/elec/packages/ylptech-byyxx/layouts/usage/usage.kicad_pcb

## KiCad design elec/packages/ylptech-byyxx/layouts/usage/usage.kicad_pcb (2026-03-11)

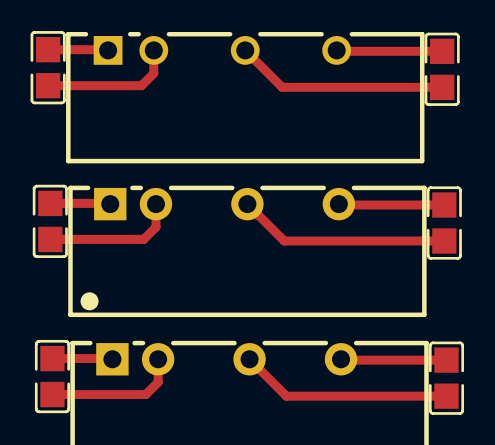
[picture p51: board elec/packages/ylptech-byyxx/layouts/usage/usage.kicad_pcb from above]

Board: 2 copper layers, 9 parts (0 on the bottom side), 12 nets.

Parts:
C1, C3, C5: 2.2µF; C0805
C2, C4, C6: 10µF; C0805
U1, U3: PWRM-TH_BXXXXS-2WR3
U2: PWRM-TH_BXXXXS-2WR2

Connections:
hv: C3.1, U2.1
lv: C3.2, U2.2
reg_5v_to_5v-power_in-hv: C1.1, U1.1
reg_5v_to_5v-power_in-lv: C1.2, U1.2
reg_5v_to_5v-power_out-hv: C2.1, U1.6
reg_5v_to_5v-power_out-lv: C2.2, U1.4
reg_12v_to_5v-power_out-hv: C4.1, U2.6
reg_12v_to_5v-power_out-lv: C4.2, U2.4
reg_24v_to_5v-power_in-hv: C5.1, U3.1
reg_24v_to_5v-power_in-lv: C5.2, U3.2
reg_24v_to_5v-power_out-hv: C6.1, U3.6
reg_24v_to_5v-power_out-lv: C6.2, U3.4
