atopile/cell-sim/elec/packages/cellsim-analog/layouts/usage/usage.kicad_pcb

## KiCad design elec/packages/cellsim-analog/layouts/usage/usage.kicad_pcb (2026-03-11)

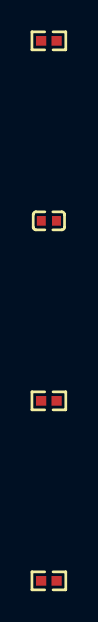
[picture p52: board elec/packages/cellsim-analog/layouts/usage/usage.kicad_pcb from above]

Board: 2 copper layers, 4 parts (0 on the bottom side), 3 nets, no tracks yet.

Parts:
C1: 1.5nF; C0402
R1: 5.1kΩ; R0402
R2: 20kΩ; R0402
R3: 1kΩ; R0402

Connections:
hv: C1.1, R3.2
lv: C1.2, R1.2
output: R1.1, R2.2, R3.1
