atopile/cell-sim/elec/packages/ti-ina228/layouts/usage/usage.kicad_pcb

## KiCad design elec/packages/ti-ina228/layouts/usage/usage.kicad_pcb (2026-03-11)

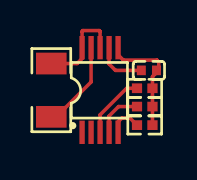
[picture p53: board elec/packages/ti-ina228/layouts/usage/usage.kicad_pcb from above]

Board: 2 copper layers, 6 parts (0 on the bottom side), 7 nets.

Parts:
C1: 100nF; C0402
R1, R2, R3: 10kΩ; R0402
R4: 150mΩ; R1206
U1: VSSOP-10_L3.0-W3.0-P0.50-LS4.9-BL

Connections:
ALERT: R1.1, U1.3
SCL: R2.1, U1.5
SDA: R3.1, U1.4
hv: C1.1, R1.2, R2.2, R3.2, U1.6
lv: C1.2, U1.1, U1.2, U1.7
rail_in_P: R4.1, U1.8, U1.10
rail_out_N: R4.2, U1.9
